3XAY/3XAY_HackPad/Images/V3.5/finishedCaseTopDown.png

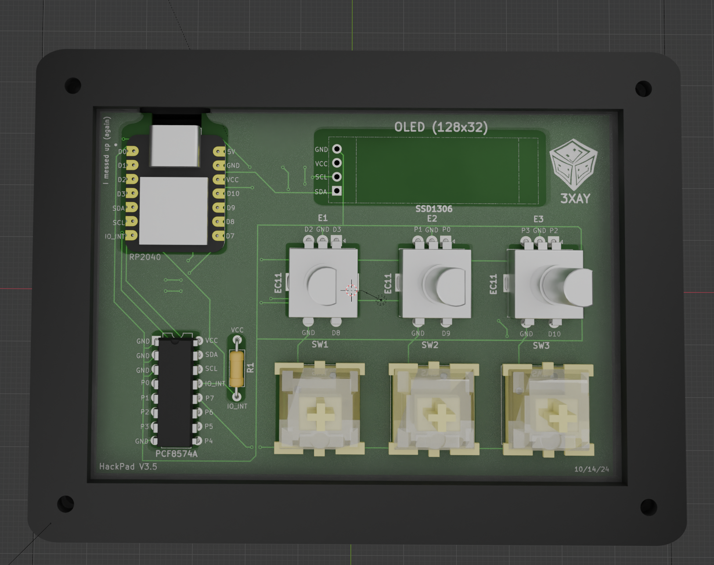
Images/V3.5/finishedCaseTopDown.png
