3XAY/3XAY_HackPad/Images/V3.5/PCB3DViewBack.png

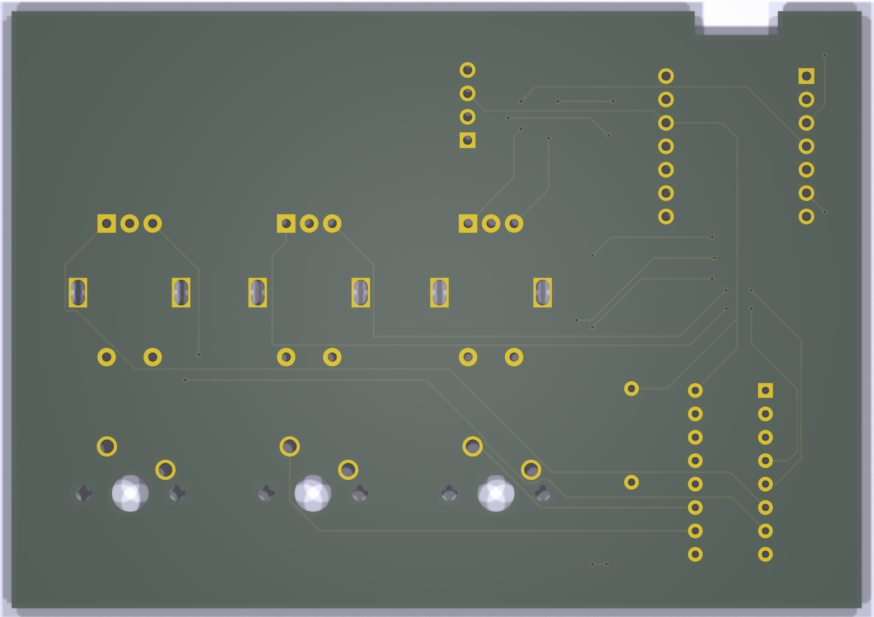
Images/V3.5/PCB3DViewBack.png
