3XAY/3XAY_HackPad/Images/V3.5/unfinishedCaseTopDown.png

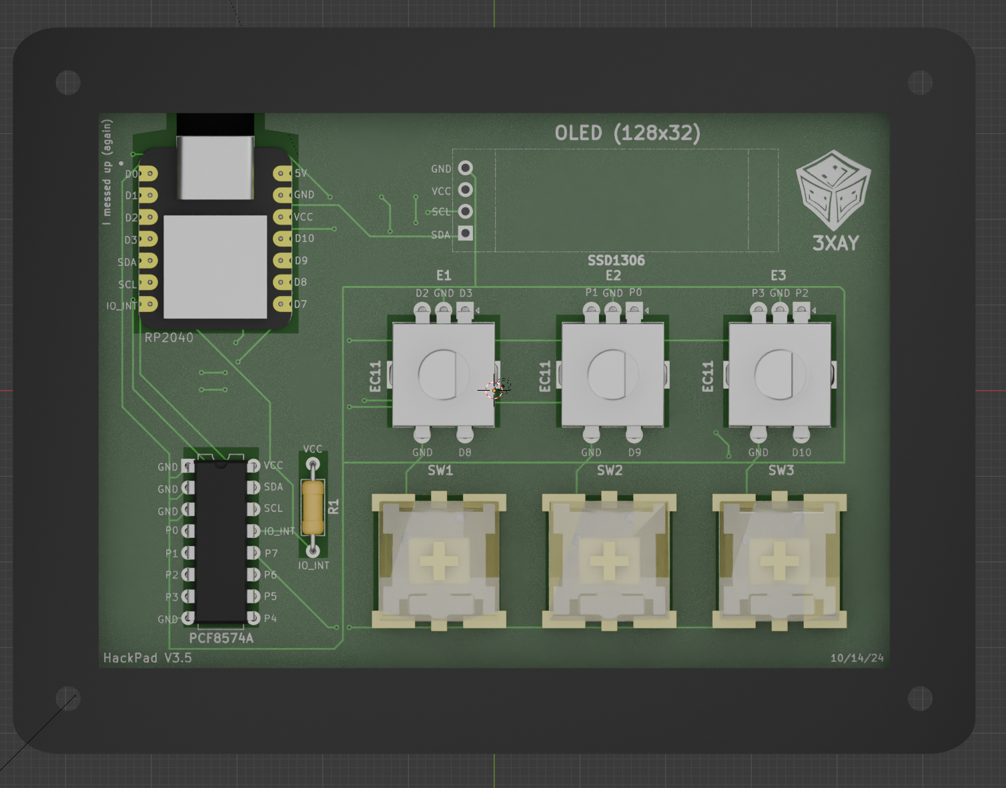
Images/V3.5/unfinishedCaseTopDown.png
