3XAY/3XAY_HackPad/Blender/PCBBackMaterial.png

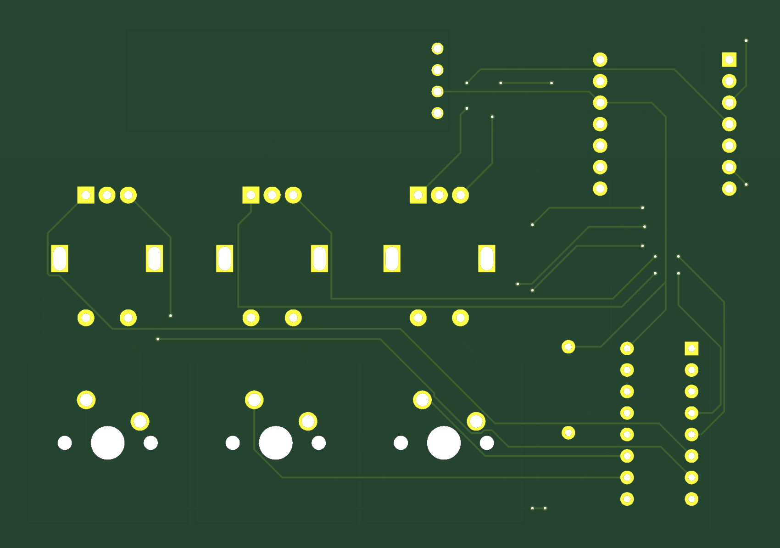
Blender/PCBBackMaterial.png
