3XAY/3XAY_HackPad/Blender/PCBFrontMaterial.png

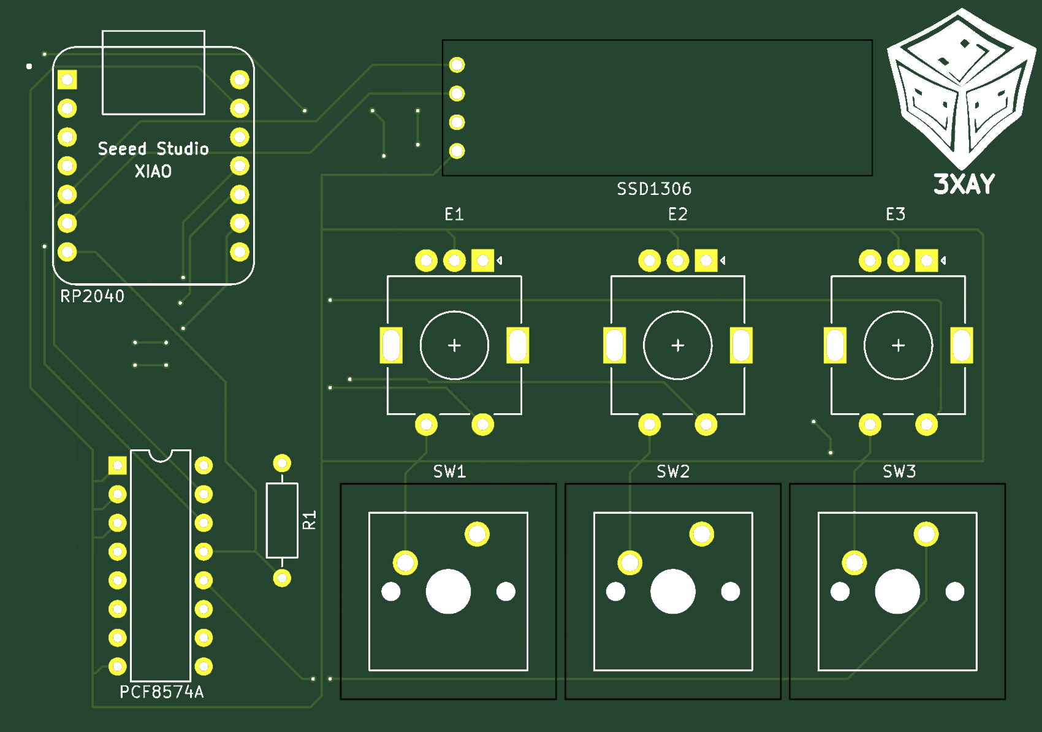
Blender/PCBFrontMaterial.png
